rockola/triton-delay/images/triton-delay-v2-3_1-silkscreen-back.png

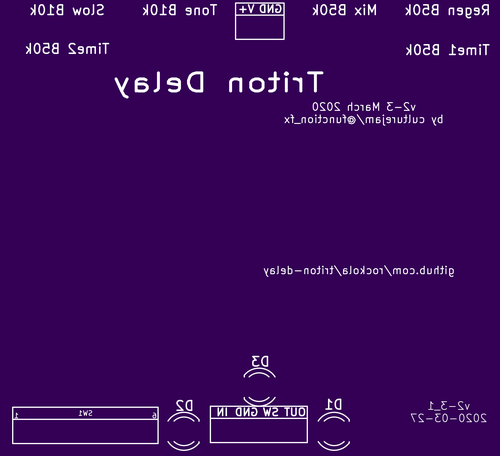
images/triton-delay-v2-3_1-silkscreen-back.png
