rockola/triton-delay/images/triton-delay-v2-3_1-silkscreen-front.png

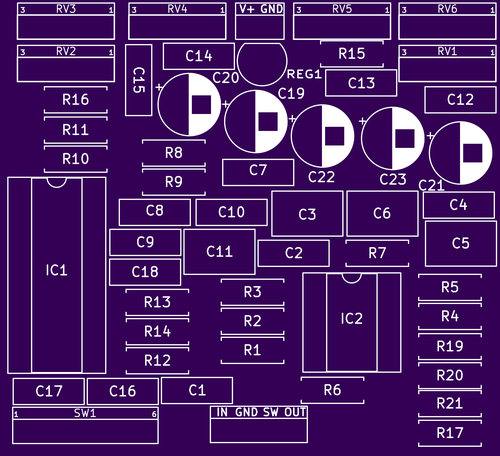
images/triton-delay-v2-3_1-silkscreen-front.png
