rockola/triton-delay/images/triton-delay-v2-3_1-soldermask-back.png

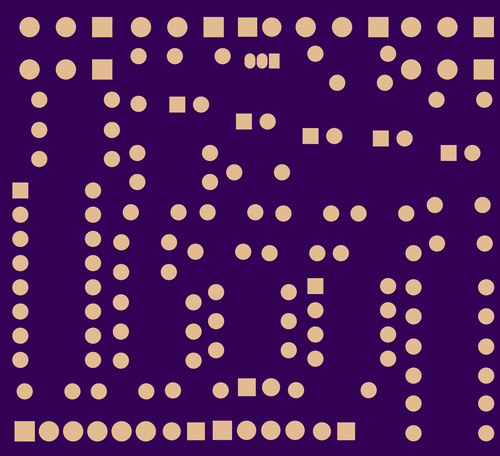
images/triton-delay-v2-3_1-soldermask-back.png
